KionoKitse/Solar-HydroBeacon-P08_00_01/P08_01_00 Thingverse CAD/cute_caterpillar/images/3e02d21fd62a3410318a6214605a6015_preview_featured.jpg

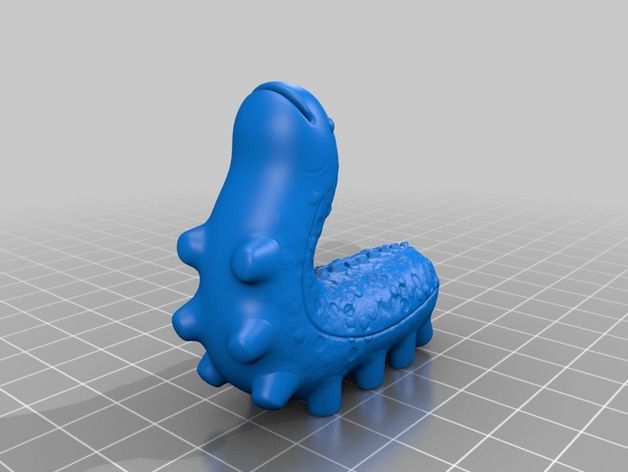
P08_01_00 Thingverse CAD/cute_caterpillar/images/3e02d21fd62a3410318a6214605a6015_preview_featured.jpg
