KionoKitse/Solar-HydroBeacon-P08_00_01/P08_01_00 Thingverse CAD/cute_caterpillar/images/43b41d4f298617752940522a6ffd2df6_preview_featured.jpg

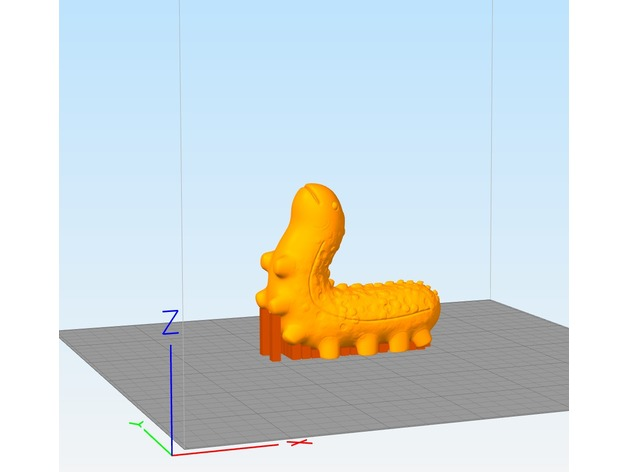
P08_01_00 Thingverse CAD/cute_caterpillar/images/43b41d4f298617752940522a6ffd2df6_preview_featured.jpg
