KionoKitse/Solar-HydroBeacon-P08_00_01/P08_01_00 Thingverse CAD/cute_caterpillar/images/67aa9c3587b258f5a7026249ae596d1a_preview_featured.jpeg

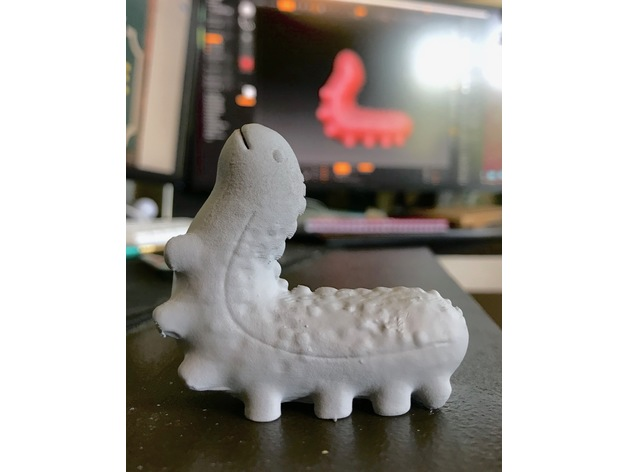
P08_01_00 Thingverse CAD/cute_caterpillar/images/67aa9c3587b258f5a7026249ae596d1a_preview_featured.jpeg
