KionoKitse/Solar-HydroBeacon-P08_00_01/P08_01_00 Thingverse CAD/Neko_Submarine/images/6c908721442afb09a18d848d62599107_preview_featured.jpg

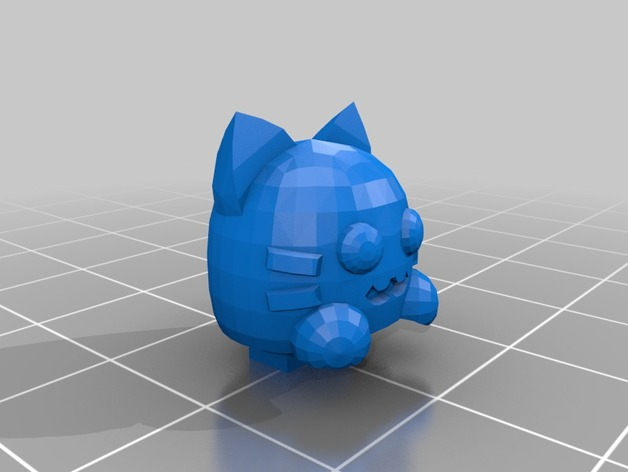
P08_01_00 Thingverse CAD/Neko_Submarine/images/6c908721442afb09a18d848d62599107_preview_featured.jpg
