KionoKitse/Solar-HydroBeacon-P08_00_01/P08_01_00 Thingverse CAD/Neko_Submarine/images/366afbdf2e312fd1846bc584daeb09b8_preview_featured.jpg

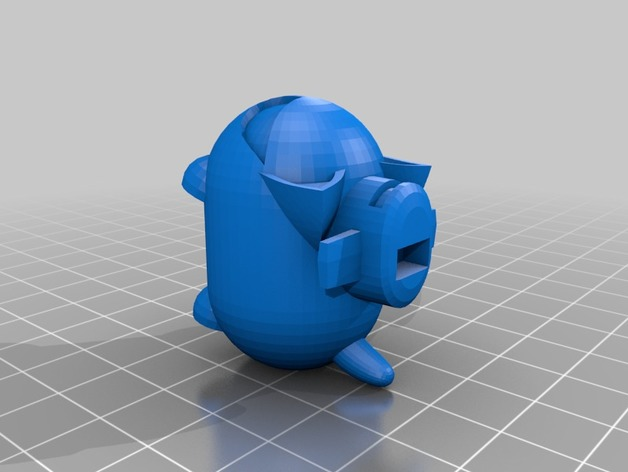
P08_01_00 Thingverse CAD/Neko_Submarine/images/366afbdf2e312fd1846bc584daeb09b8_preview_featured.jpg
