KionoKitse/Solar-HydroBeacon-P08_00_01/P08_01_00 Thingverse CAD/Neko_Submarine/images/5813bd414e4b4446a906540db2377fc1_preview_featured.jpg

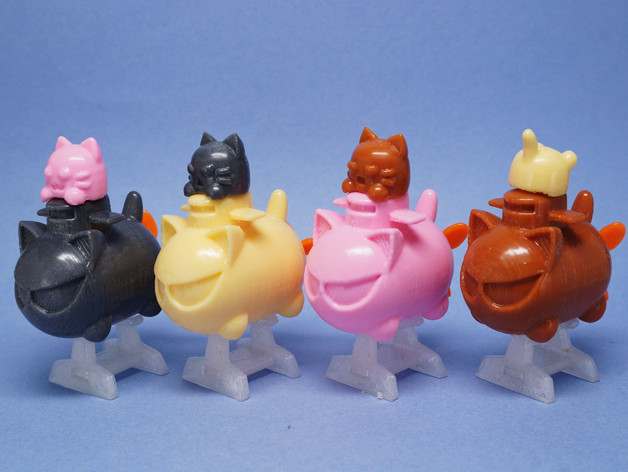
P08_01_00 Thingverse CAD/Neko_Submarine/images/5813bd414e4b4446a906540db2377fc1_preview_featured.jpg
