KionoKitse/Solar-HydroBeacon-P08_00_01/P08_01_00 Thingverse CAD/Neko_Submarine/images/65110ef296dd14ffac49d6ea55c07fd1_preview_featured.jpg

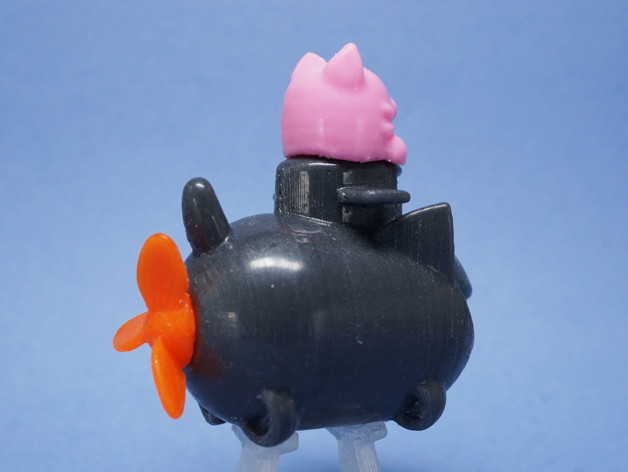
P08_01_00 Thingverse CAD/Neko_Submarine/images/65110ef296dd14ffac49d6ea55c07fd1_preview_featured.jpg
