KionoKitse/Solar-HydroBeacon-P08_00_01/P08_01_00 Thingverse CAD/Neko_Submarine/images/9429286c05328b340de6d6a362c487be_preview_featured.jpg

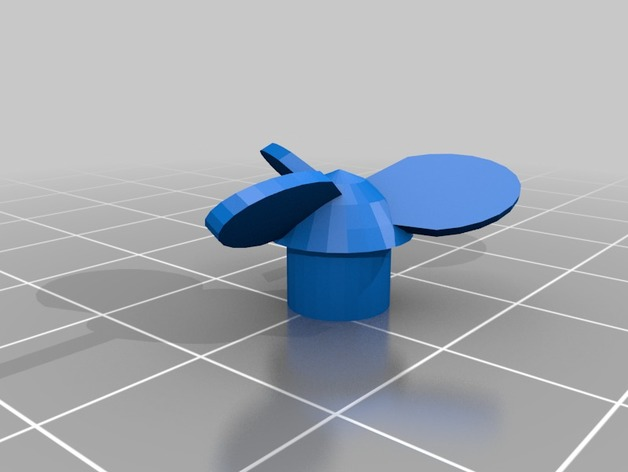
P08_01_00 Thingverse CAD/Neko_Submarine/images/9429286c05328b340de6d6a362c487be_preview_featured.jpg
