KionoKitse/Solar-HydroBeacon-P08_00_01/P08_01_00 Thingverse CAD/Neko_Submarine/images/a352465f42ce8da5f80c4f37c28ce8e0_preview_featured.jpg

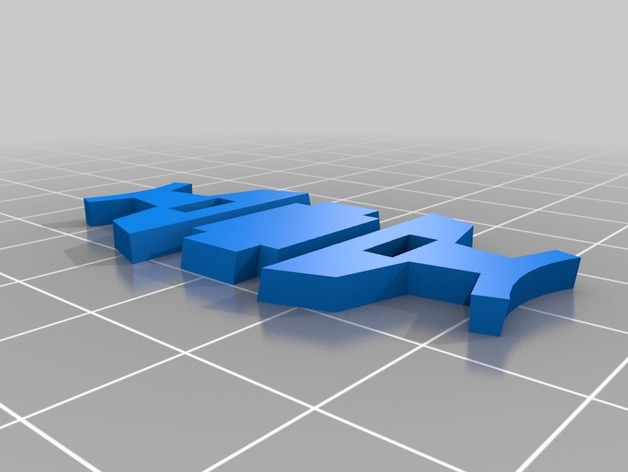
P08_01_00 Thingverse CAD/Neko_Submarine/images/a352465f42ce8da5f80c4f37c28ce8e0_preview_featured.jpg
