KionoKitse/Solar-HydroBeacon-P08_00_01/P08_01_00 Thingverse CAD/Neko_Submarine/images/bf654b6abbde9b80a3a1970df4d1c9a6_preview_featured.jpg

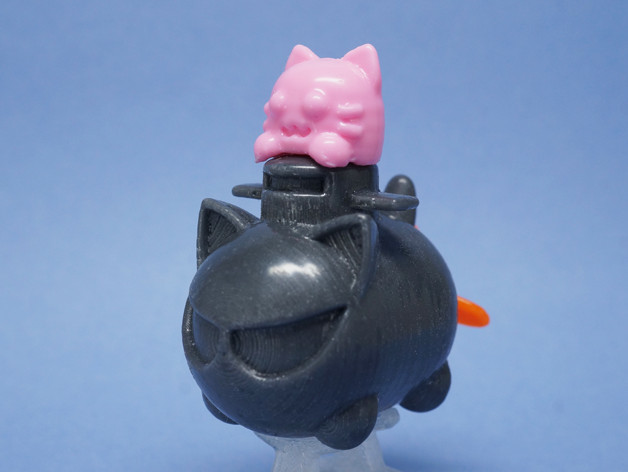
P08_01_00 Thingverse CAD/Neko_Submarine/images/bf654b6abbde9b80a3a1970df4d1c9a6_preview_featured.jpg
